Uberi/SeventhSense/Pictures/2014-02-22 00.40.36.jpg

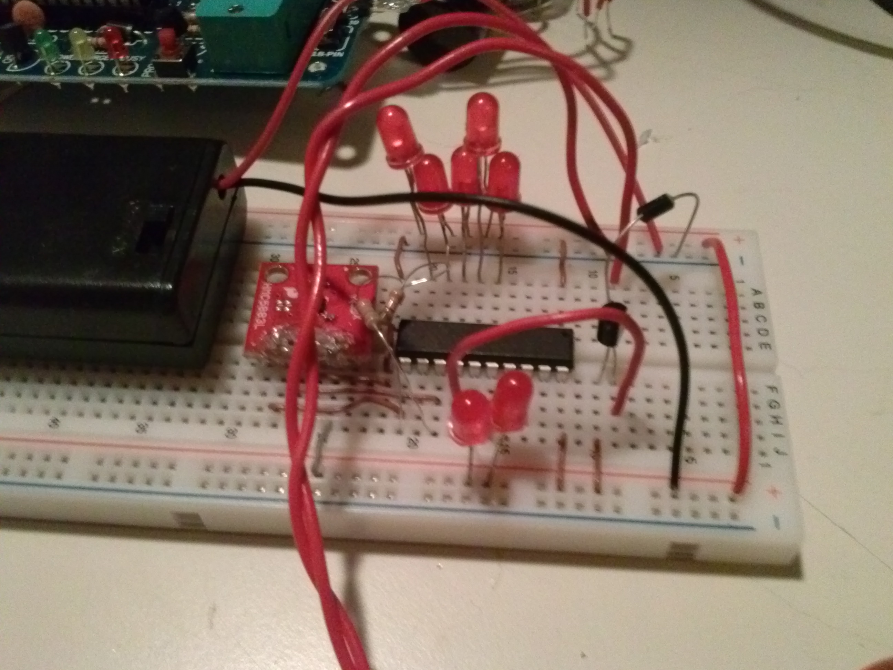
Pictures/2014-02-22 00.40.36.jpg
