Uberi/SeventhSense/Pictures/2014-02-22 16.47.20.jpg

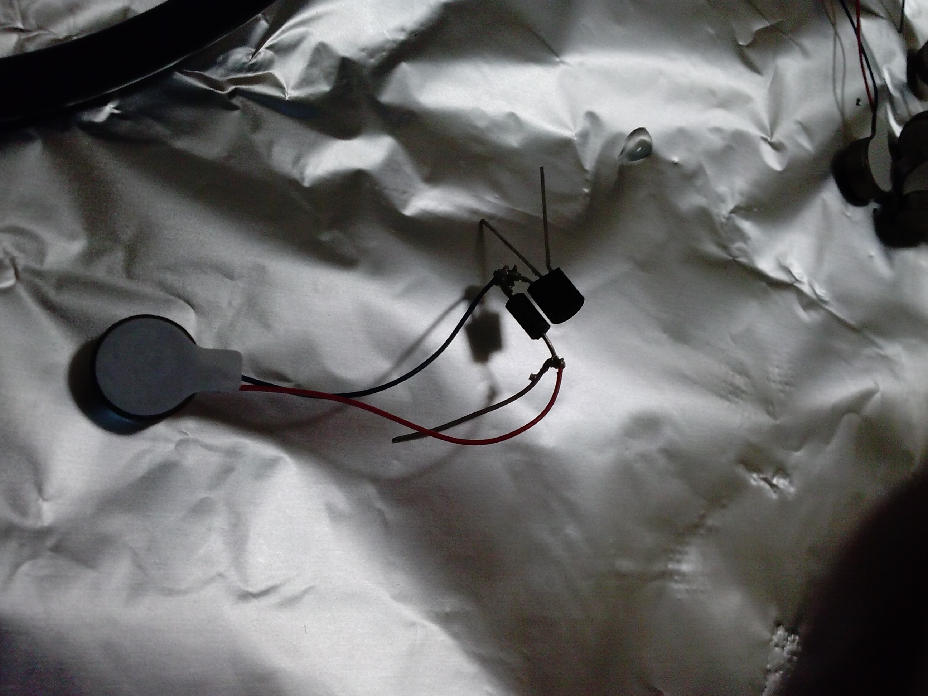
Pictures/2014-02-22 16.47.20.jpg
