Uberi/SeventhSense/Pictures/2014-02-22 17.00.14.jpg

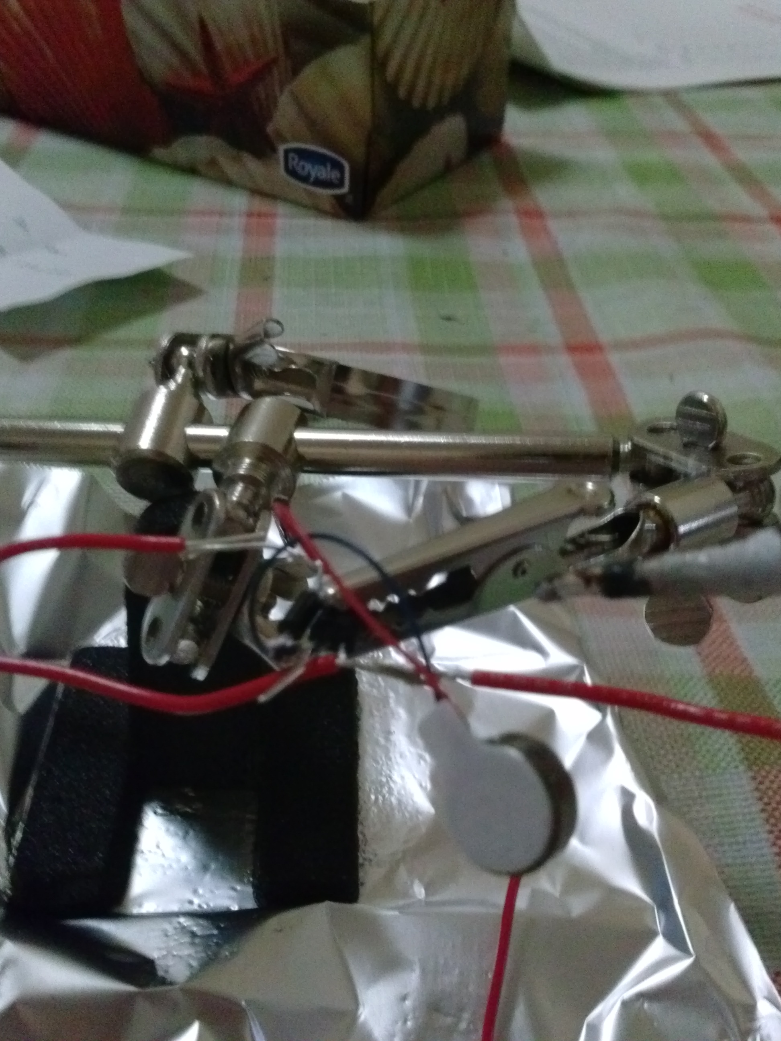
Pictures/2014-02-22 17.00.14.jpg
