Uberi/SeventhSense/Pictures/2014-02-23 20.43.22.jpg

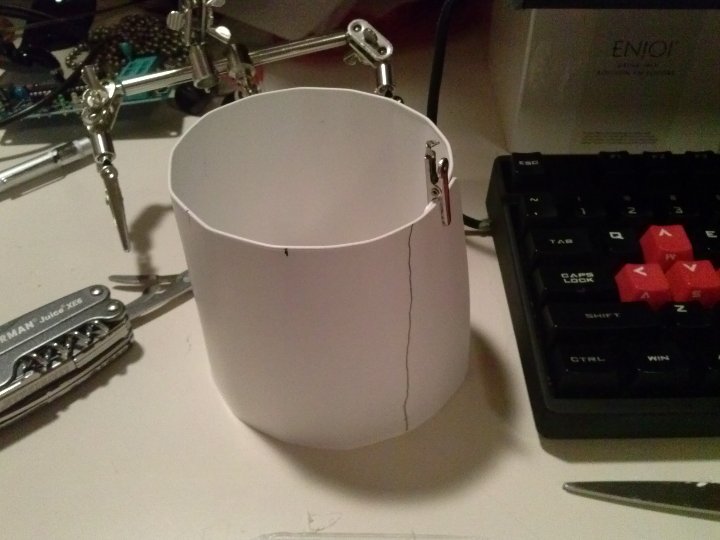
Pictures/2014-02-23 20.43.22.jpg
