Uberi/SeventhSense/Pictures/2014-03-21 01.56.20.jpg

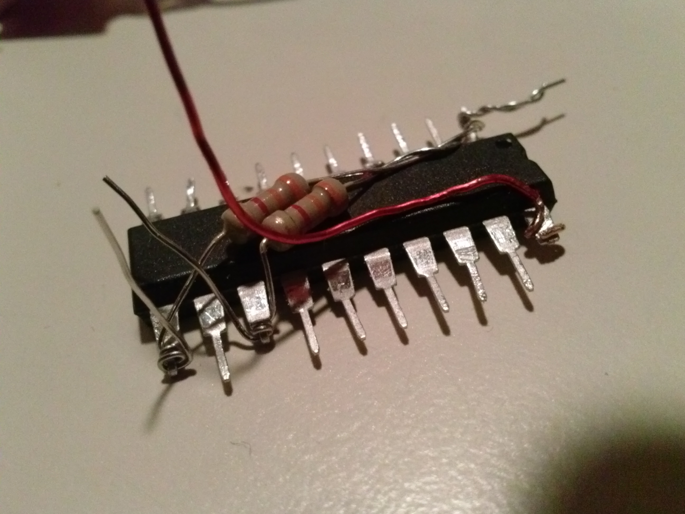
Pictures/2014-03-21 01.56.20.jpg
