Uberi/SeventhSense/Pictures/2014-03-24 00.42.39.jpg

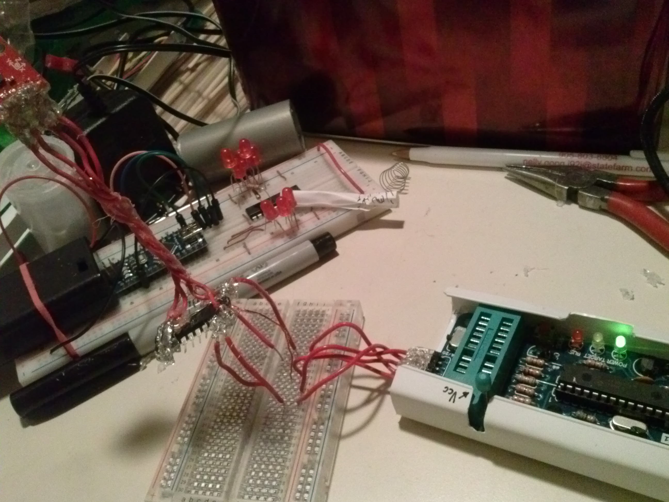
Pictures/2014-03-24 00.42.39.jpg
