Uberi/SeventhSense/Pictures/2014-03-24 00.43.12.jpg

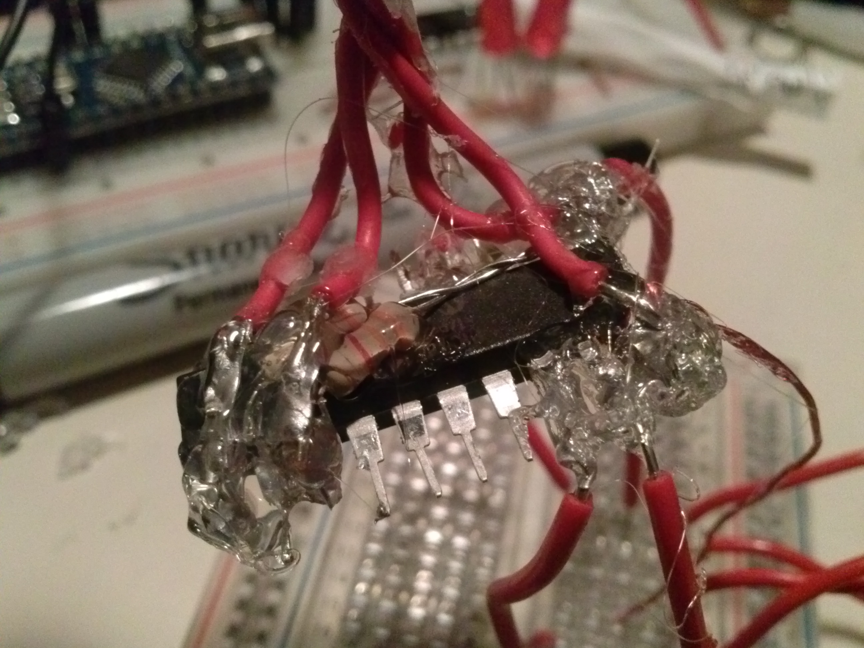
Pictures/2014-03-24 00.43.12.jpg
