Uberi/SeventhSense/HMC5883/Triple Axis Magnetometer - HMC5883L Breakout Quickstart Guide - SparkFun Electronics_files/5883L_BoB-small.jpg

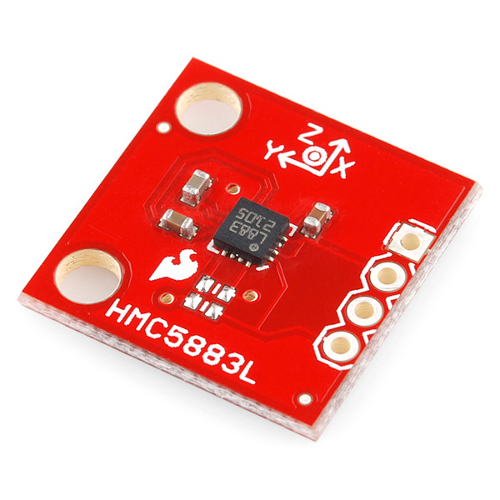
HMC5883/Triple Axis Magnetometer - HMC5883L Breakout Quickstart Guide - SparkFun Electronics_files/5883L_BoB-small.jpg
