Uberi/SeventhSense/HMC5883/Triple Axis Magnetometer - HMC5883L Breakout Quickstart Guide - SparkFun Electronics_files/Arduino_HMC5883_xyz-small.jpg

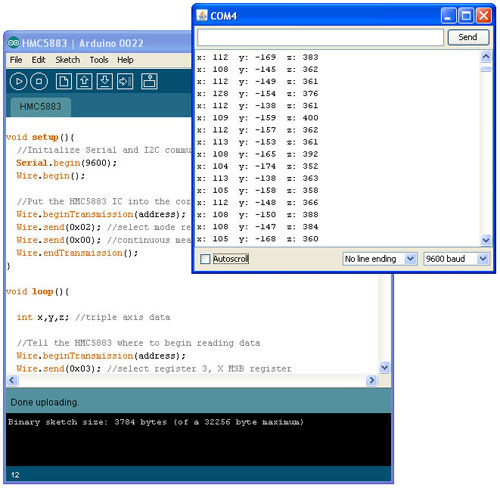
HMC5883/Triple Axis Magnetometer - HMC5883L Breakout Quickstart Guide - SparkFun Electronics_files/Arduino_HMC5883_xyz-small.jpg
