Uberi/SeventhSense/HMC5883/Triple Axis Magnetometer - HMC5883L Breakout Quickstart Guide - SparkFun Electronics_files/hmc5883Fritz-small.jpg

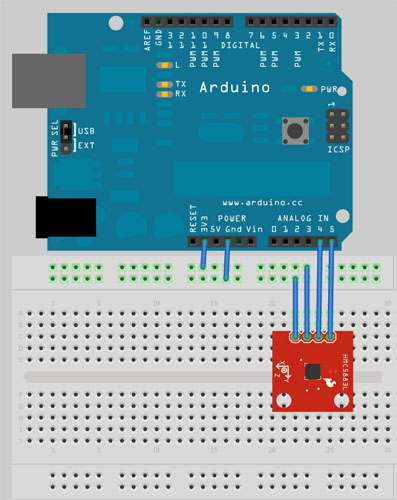
HMC5883/Triple Axis Magnetometer - HMC5883L Breakout Quickstart Guide - SparkFun Electronics_files/hmc5883Fritz-small.jpg
